martinwork/pxt-coderdojo-controller/hardware/CAD Images/copper_layer_2_bottom.png

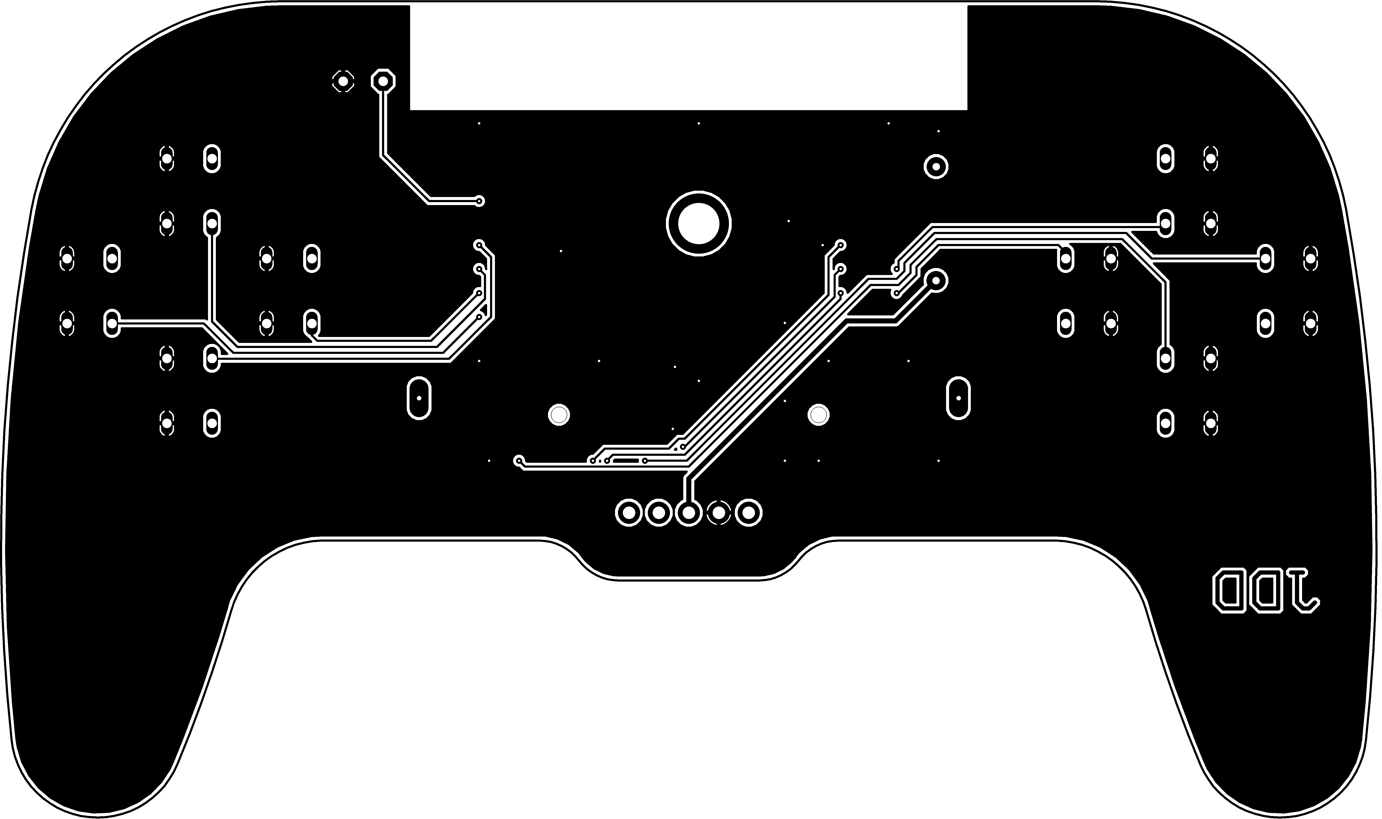
hardware/CAD Images/copper_layer_2_bottom.png
