martinwork/pxt-coderdojo-controller/hardware/CAD Images/layout.png

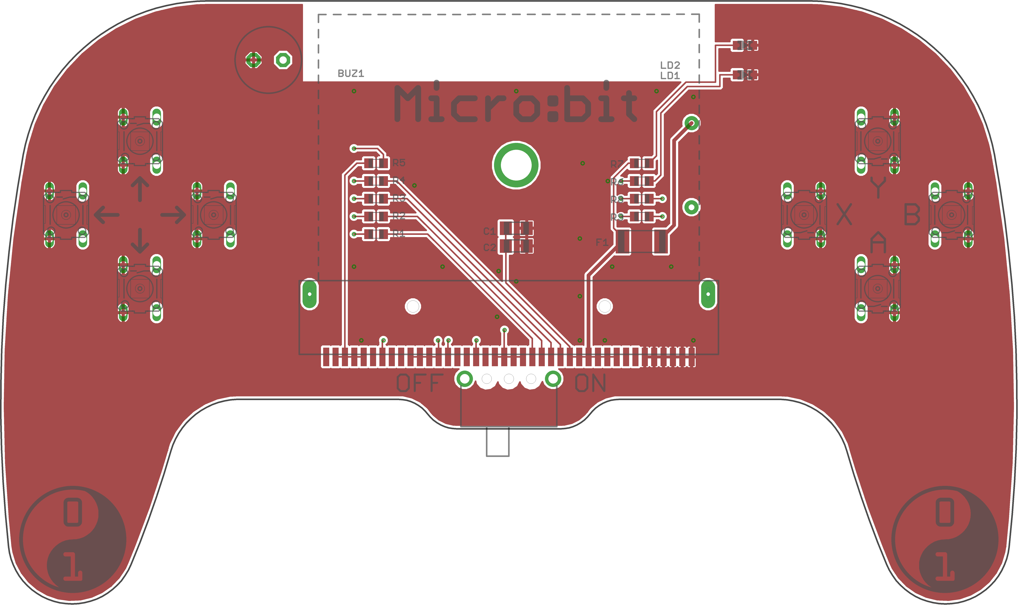
hardware/CAD Images/layout.png
