martinwork/pxt-coderdojo-controller/hardware/CAD Images/PCB 3D.png

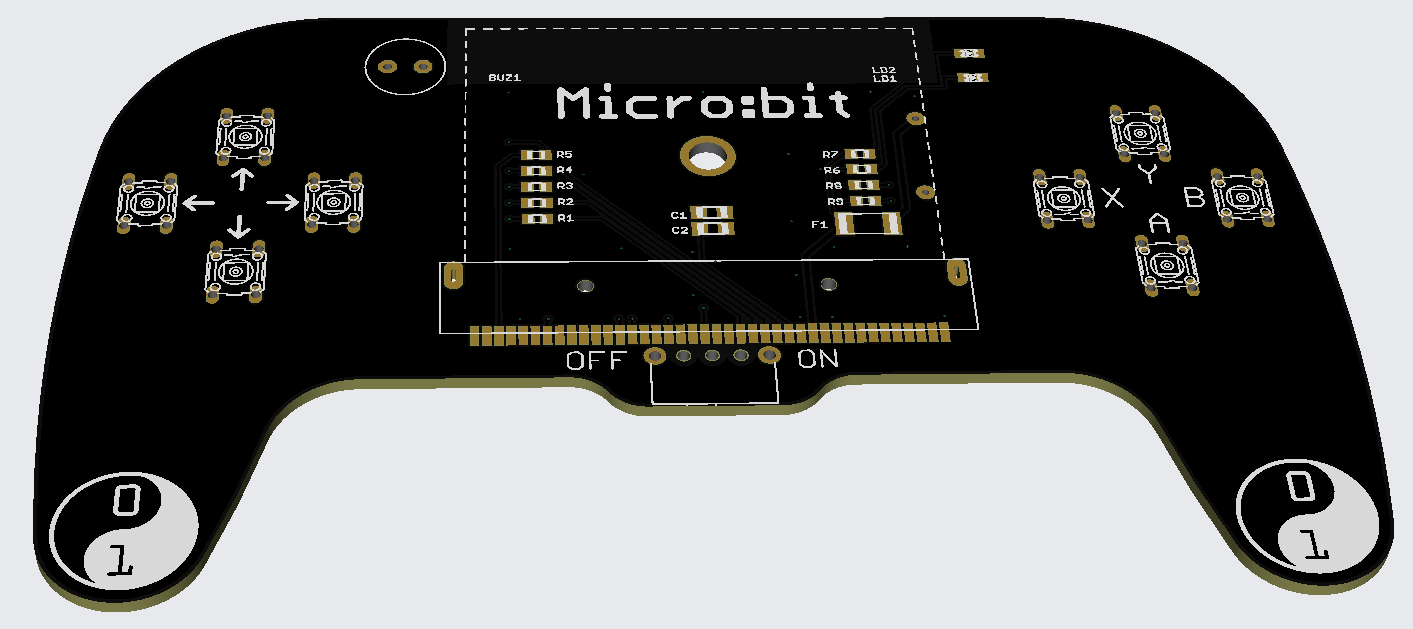
hardware/CAD Images/PCB 3D.png
