martinwork/pxt-coderdojo-controller/images/Back.jpg

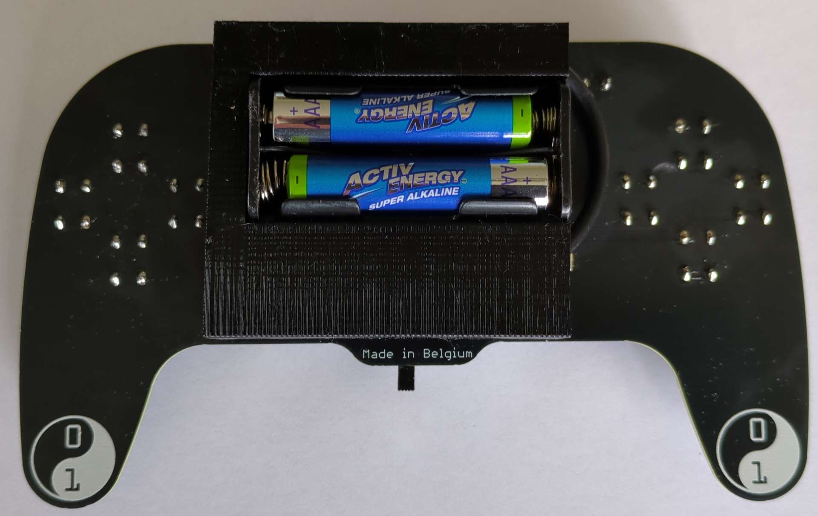
images/Back.jpg
