martinwork/pxt-coderdojo-controller/images/CoderDojo Controller.png

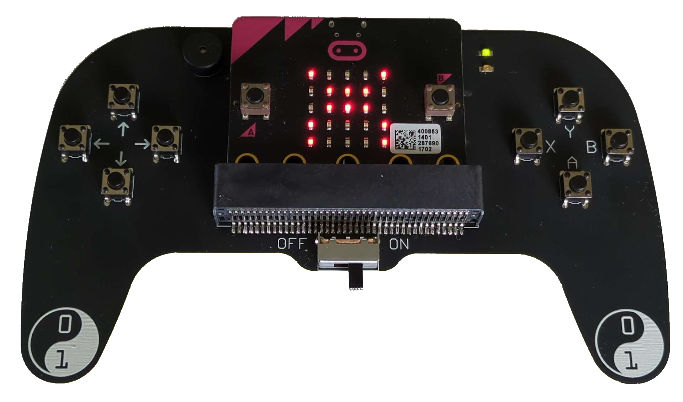
images/CoderDojo Controller.png
