martinwork/pxt-coderdojo-controller/images/Front angle.jpg

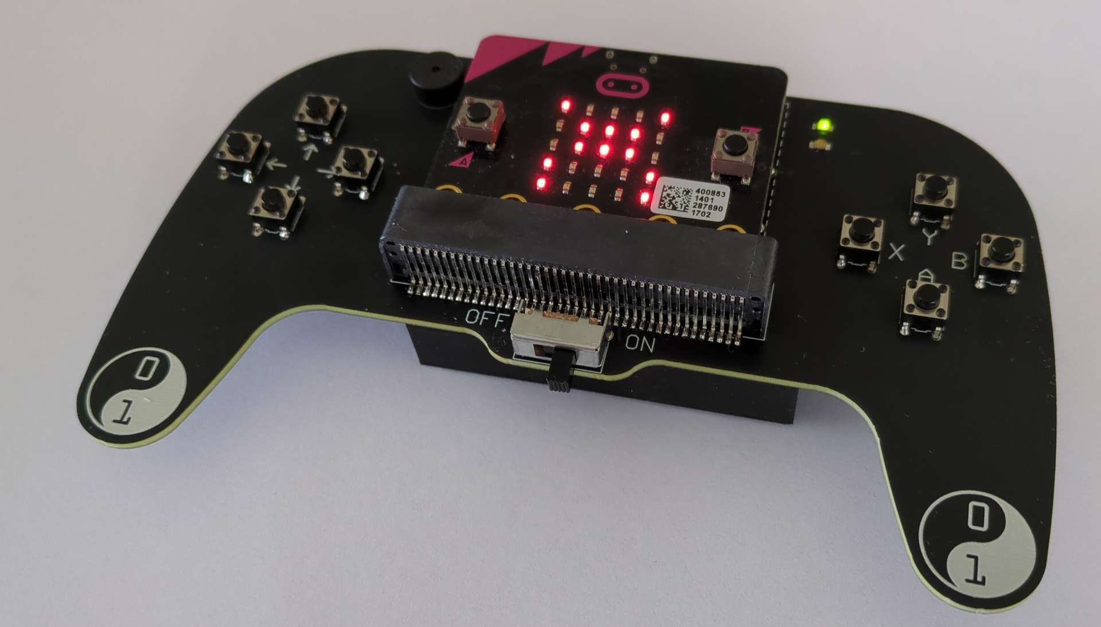
images/Front angle.jpg
