martinwork/pxt-coderdojo-controller/images/Front.jpg

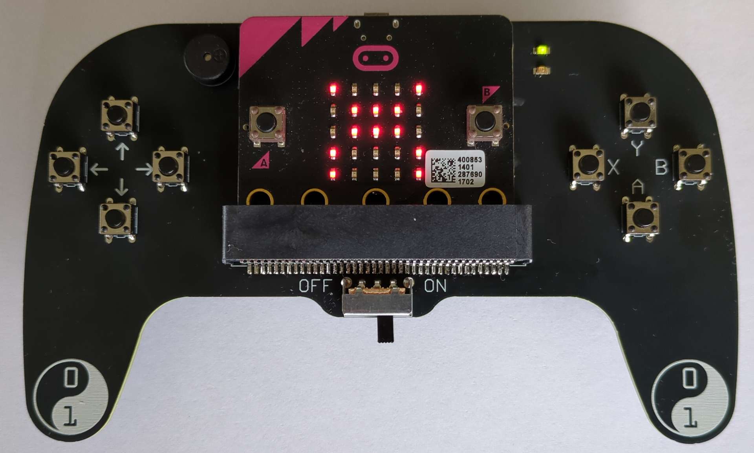
images/Front.jpg
