martinwork/pxt-coderdojo-controller/images/Makecode blocks.png

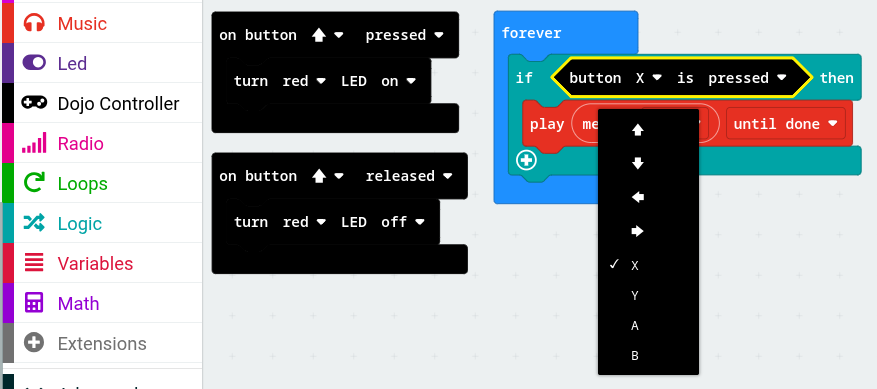
images/Makecode blocks.png
